mihranrazaa/WayBoard/Assets/dxf.png

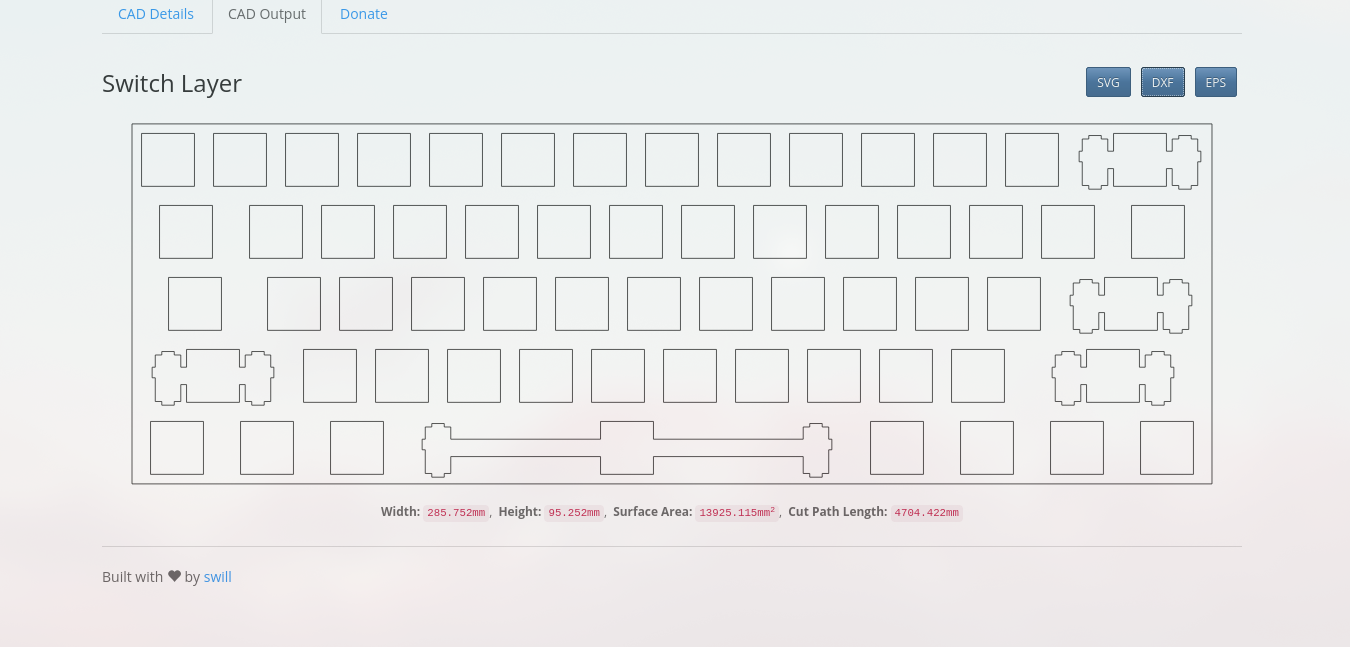
Assets/dxf.png
