mihranrazaa/WayBoard/Assets/fk.png

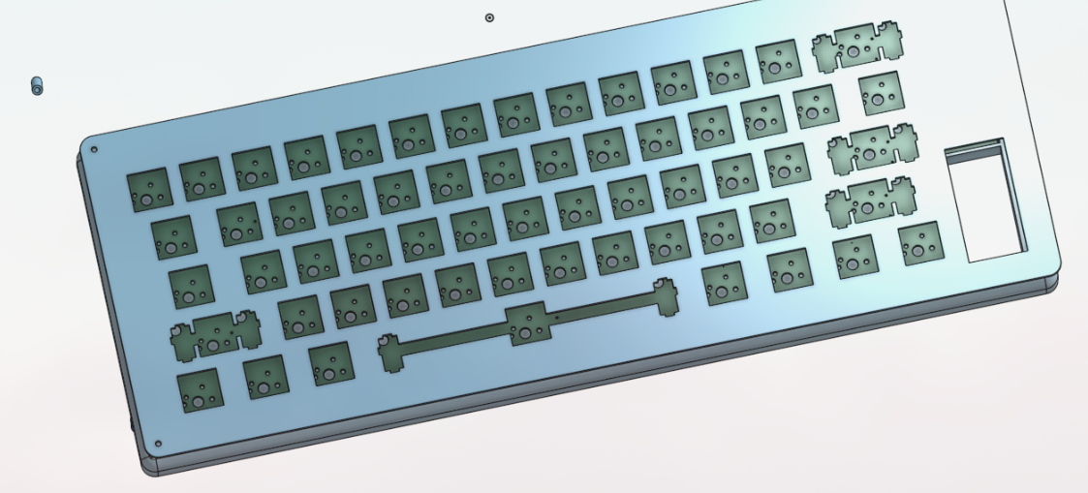
Assets/fk.png
